Gallard88/PWM_Controller/firmware/adc.h

/** @package

	adc.h

	Copyright(c) Toshiba 2000

	Author: TOM BURNS
	Created: TB  26/01/2013 12:43:36 PM
	Last change: TB 26/01/2013 12:46:49 PM
*/
//*****************************************************************************
#ifndef __ADC_H__
#define __ADC_H__
//*****************************************************************************

void ADC_Init(void);

int ADC_Read(int ch);

//*****************************************************************************
//*****************************************************************************
#endif
