Gallard88/PWM_Controller/firmware/CmdProcessor.h

//*****************************************************************************
#ifndef __CMD_PROCESSOR__
#define __CMD_PROCESSOR__
//*****************************************************************************
const struct cmdtable
{
  const char * const cmd;
  int (*func)(char *buf);
};

char *Cmd_SkipSpace(char *ptr);

char *Cmd_SkipChars(char *ptr);

int Cmd_Lookup(const struct cmdtable *tbl, char *line);

//*****************************************************************************
//*****************************************************************************
#endif
